nicoles/OpeNITHM/v2-cad/side_spacer_3mm_clear.dxf

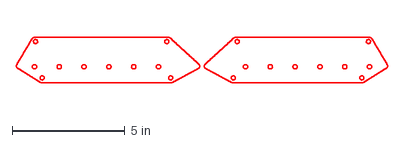
[picture p16: CAD file, 2020-05-24]
v2-cad/side_spacer_3mm_clear.dxf
16.5 x 2.01 in
