nicoles/OpeNITHM/v2-cad/side_backs_3mm_black.dxf

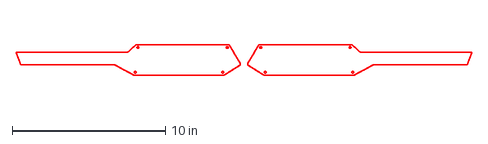
[picture p17: CAD file, 2020-05-24]
v2-cad/side_backs_3mm_black.dxf
29.8 x 2.01 in
