nicoles/OpeNITHM/v2-cad/case-model.obj

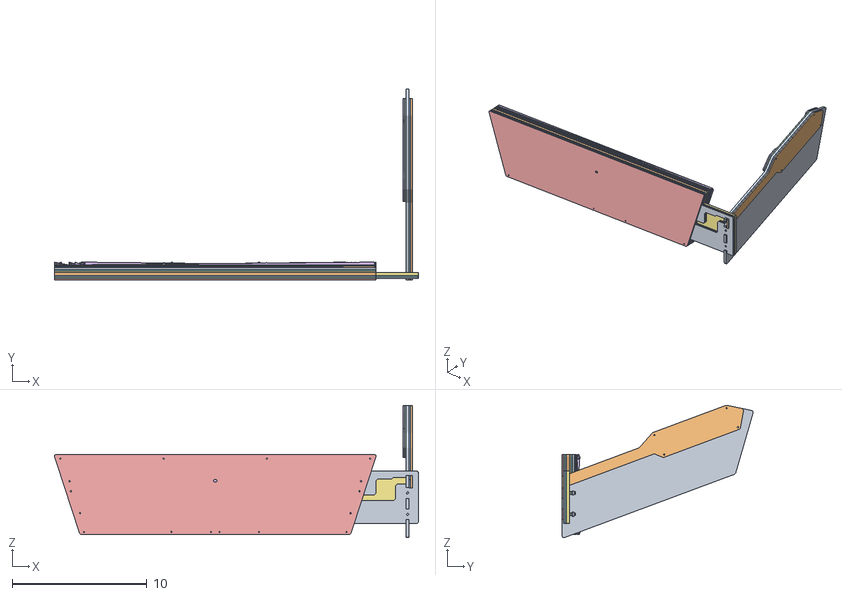
[picture p18: CAD file, 2020-05-24]
v2-cad/case-model.obj
27.0 x 14.2 x 9.81
