nicoles/OpeNITHM/Firmware/OpeNITHM/SerialLeds.h

#ifndef __SERIALLEDS_h
#define __SERIALLEDS_h

#if defined(ARDUINO) && ARDUINO >= 100
#include "arduino.h"
#else
#include "WProgram.h"
#endif
#include "Config.h"

#include <EEPROM.h>
#include <FastLED.h>

#define LIGHTS_FLAG 0xFF

extern bool updateLeds;
extern CRGB led_on;
extern CRGB led_off;

typedef struct {
  uint8_t b;
  uint8_t r;
  uint8_t g;
} RGBLed;

class SerialLeds
{
  private:
    uint8_t lastBuffer[100];

  public:
    SerialLeds();
    void saveLights();
    void loadLights();
    void processBulk(uint8_t *buf);
    RGBLed getKey(uint8_t key); // Left to Right
    RGBLed getDivider(uint8_t divider); // Left to Right

    union {
      RGBLed rgb[32];
      uint8_t raw[96];
    } ledData;
};

#endif
